airpocket-soundman/M5Stack_Stroboscope/schematics/m5stack_stroboscope/m5stack_stroboscope.kicad_sch

## KiCad design schematics/m5stack_stroboscope/m5stack_stroboscope.kicad_sch (2025-08-18)

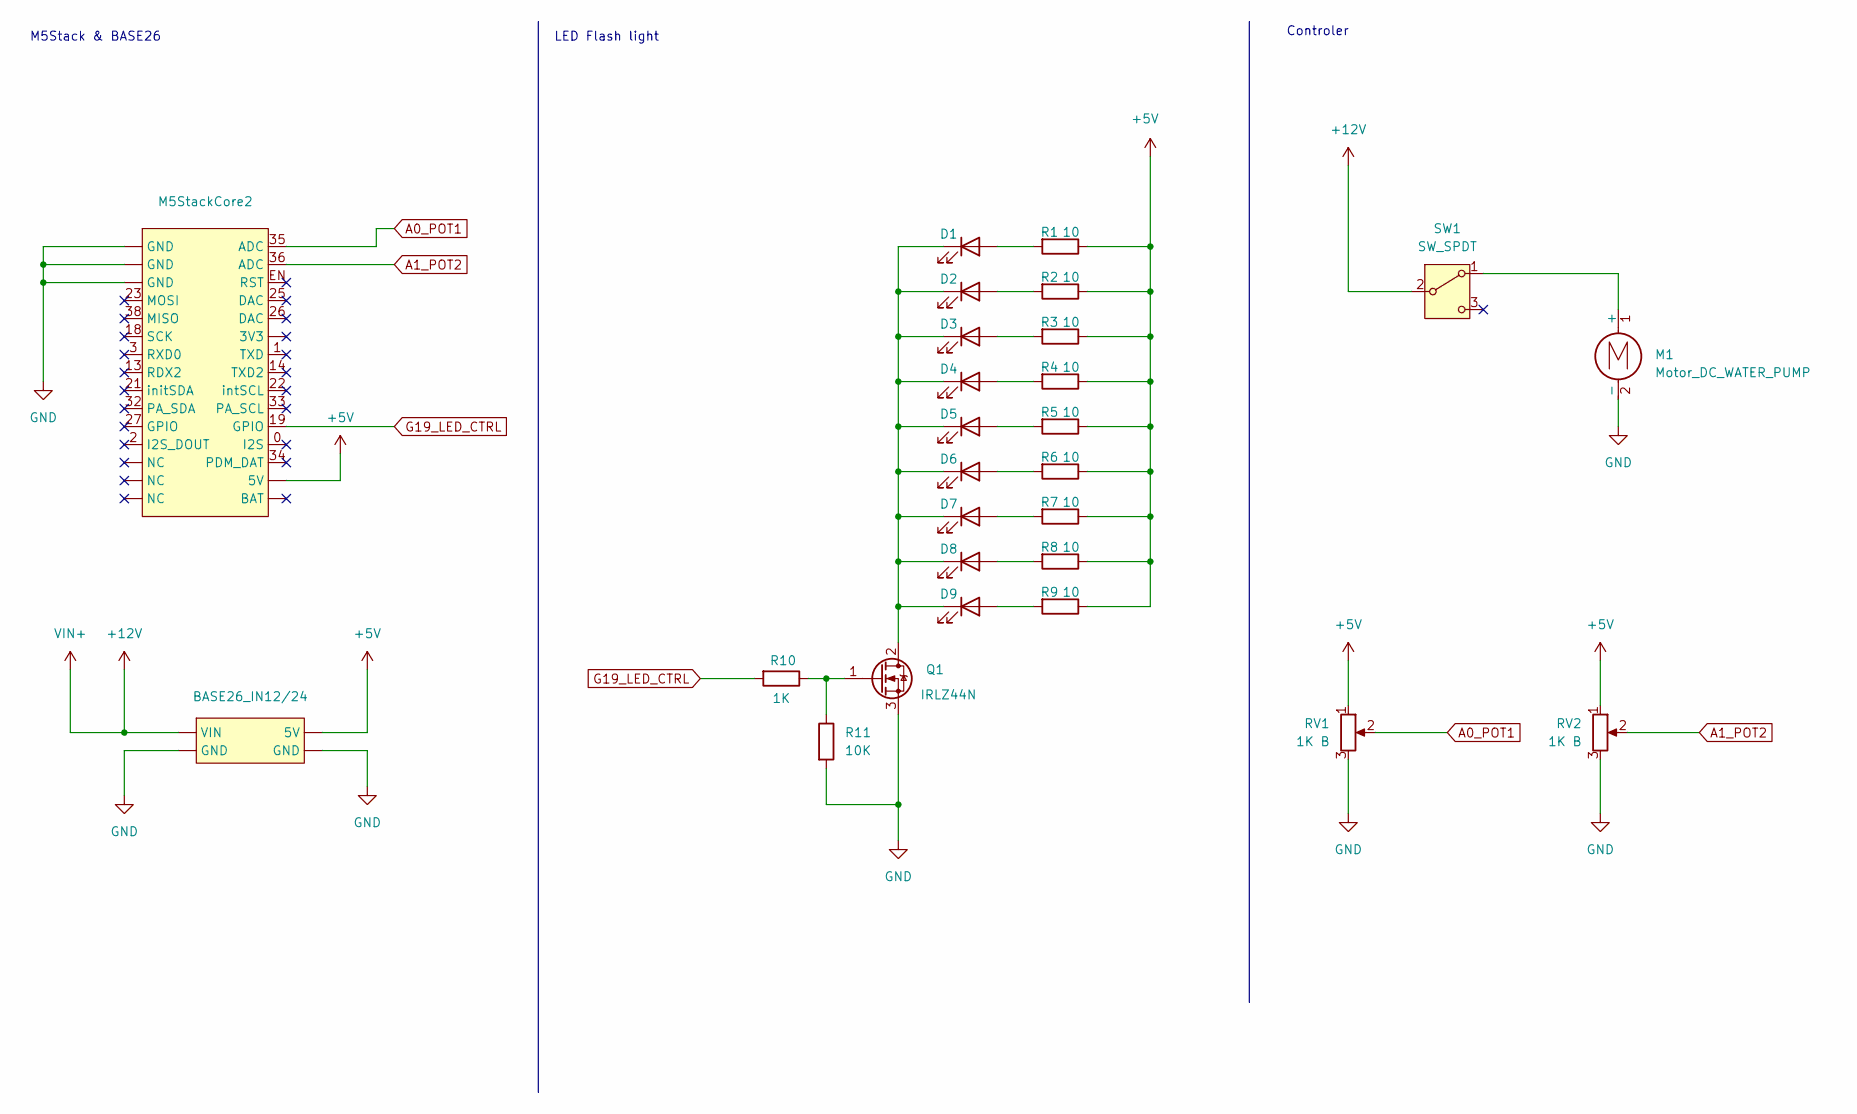
[picture p13: schematic m5stack_stroboscope.kicad_sch]

Parts:
BASE26_IN12/24: (no value)
D1, D2, D3, D4, D5, D6, D7, D8, D9: LED
M1: Motor_DC_WATER_PUMP
M5StackCore2: (no value)
Q1: IRLZ44N; TO-220-3_Vertical
R1, R2, R3, R4, R5, R6, R7, R8, R9: 10
R10: 1K
R11: 10K
RV1, RV2: 1K B
SW1: SW_SPDT

Connections:
+5V: BASE26_IN12/24., M5StackCore2. (3V3), R1.1, R2.1, R3.1, R4.1, R5.1, R6.1, R7.1, R8.1, R9.1, RV1.1, RV2.1
+12V: BASE26_IN12/24., SW1.2 (B)
A0_POT1: M5StackCore2.35 (ADC), RV1.2
A1_POT2: M5StackCore2.36 (ADC), RV2.2
G19_LED_CTRL: M5StackCore2.19 (GPIO), R10.2
GND: BASE26_IN12/24., M1.2 (-), M5StackCore2. (3V3), Q1.3 (S), R11.2, RV1.3, RV2.3
unnamed: D1.1 (K), D2.1 (K), D3.1 (K), D4.1 (K), D5.1 (K), D6.1 (K), D7.1 (K), D8.1 (K), D9.1 (K), Q1.2 (D)
unnamed: D1.2 (A), R1.2
unnamed: D2.2 (A), R2.2
unnamed: D3.2 (A), R3.2
unnamed: D4.2 (A), R4.2
unnamed: D5.2 (A), R5.2
unnamed: D6.2 (A), R6.2
unnamed: D7.2 (A), R7.2
unnamed: D8.2 (A), R8.2
unnamed: D9.2 (A), R9.2
unnamed: M1.1 (+), SW1.1 (A)
unnamed: Q1.1 (G), R10.1, R11.1

Notes on the sheet:
M5Stack & BASE26
Controler
LED Flash light
